HuskieRobotics/HuskieBoardPublic/Eagle CAD/projects/HuskieBoard/PthHeaderAssy.png

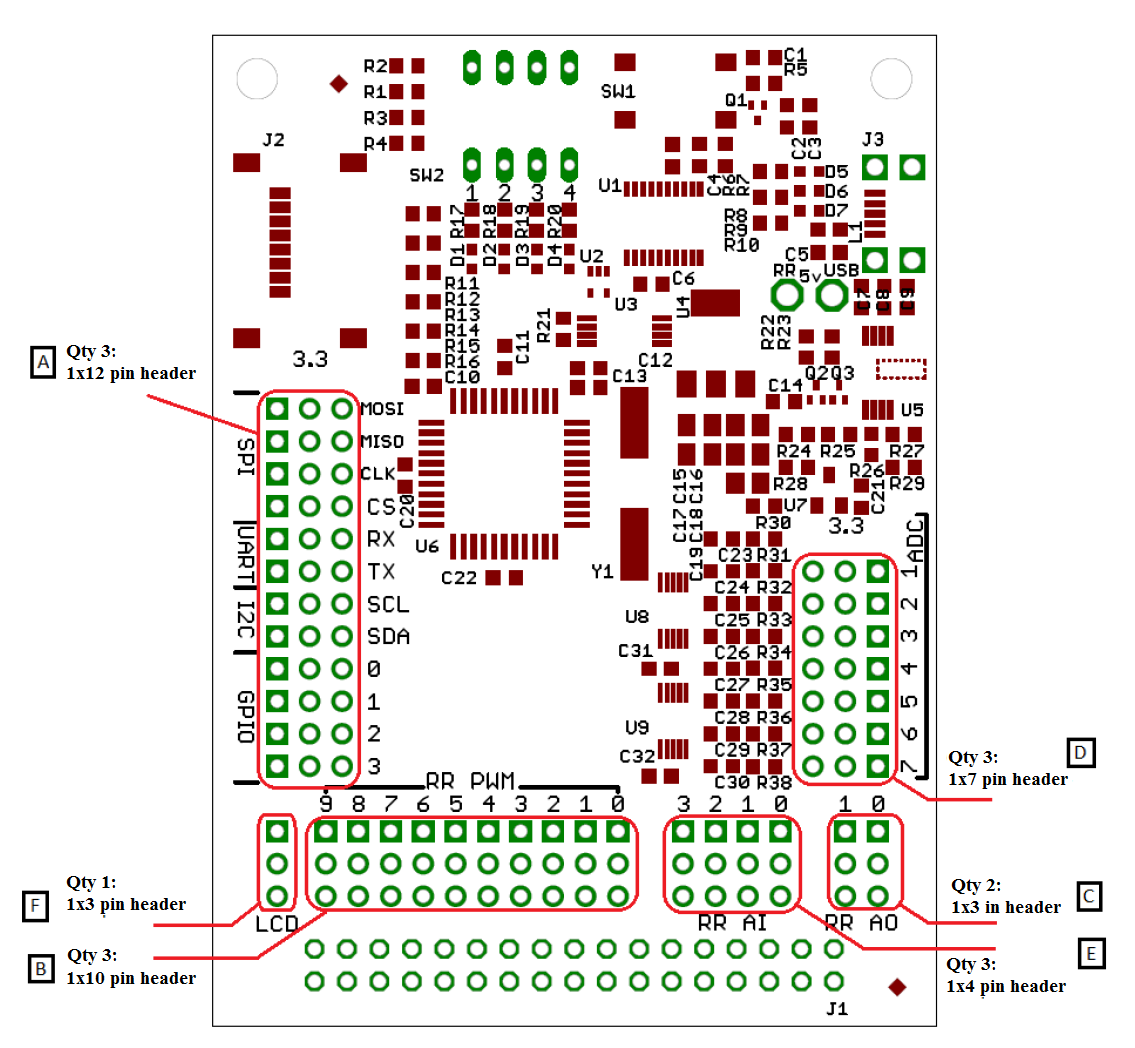
Eagle CAD/projects/HuskieBoard/PthHeaderAssy.png
