HuskieRobotics/HuskieBoardPublic/LabView/LabVIEW API/Examples/LED Example/HB__OpenHuskieBoardp.png

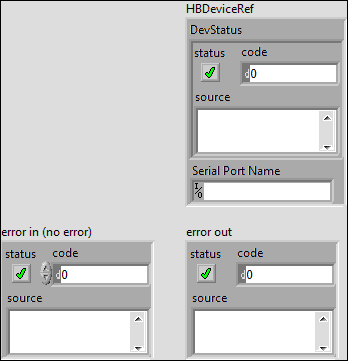
LabView/LabVIEW API/Examples/LED Example/HB__OpenHuskieBoardp.png
