HuskieRobotics/HuskieBoardPublic/LabView/LabVIEW API/Huskie Board/HuskieBoard API Doc/HB_CheckChecksum/HB__CheckChecksumd.png

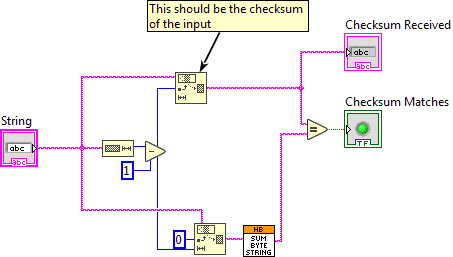
LabView/LabVIEW API/Huskie Board/HuskieBoard API Doc/HB_CheckChecksum/HB__CheckChecksumd.png
