HuskieRobotics/HuskieBoardPublic/LabView/LabVIEW API/Huskie Board/HuskieBoard API Doc/HB_CloseHuskieBoard/HB__CloseHuskieBoardh.png

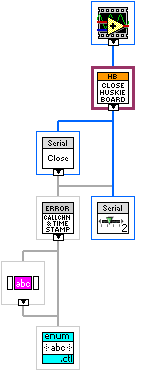
LabView/LabVIEW API/Huskie Board/HuskieBoard API Doc/HB_CloseHuskieBoard/HB__CloseHuskieBoardh.png
