HuskieRobotics/HuskieBoardPublic/LabView/LabVIEW API/Huskie Board/HuskieBoard API Doc/HB_CloseHuskieBoard/HB__CloseHuskieBoardp.png

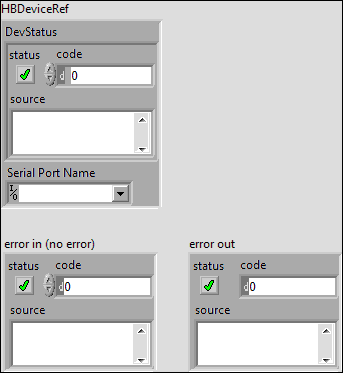
LabView/LabVIEW API/Huskie Board/HuskieBoard API Doc/HB_CloseHuskieBoard/HB__CloseHuskieBoardp.png
