HuskieRobotics/HuskieBoardPublic/LabView/LabVIEW API/Huskie Board/HuskieBoard API Doc/HB_CloseLog/HB__CloseLogd.png

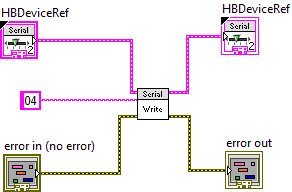
LabView/LabVIEW API/Huskie Board/HuskieBoard API Doc/HB_CloseLog/HB__CloseLogd.png
