HuskieRobotics/HuskieBoardPublic/LabView/LabVIEW API/Huskie Board/HuskieBoard API Doc/HB_CloseLog/HB__CloseLogp.png

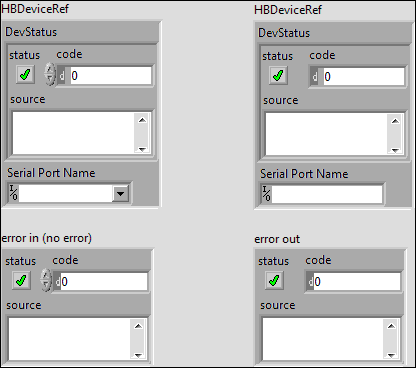
LabView/LabVIEW API/Huskie Board/HuskieBoard API Doc/HB_CloseLog/HB__CloseLogp.png
