HuskieRobotics/HuskieBoardPublic/LabView/LabVIEW API/Huskie Board/HuskieBoard API Doc/HB_ConfigureDIO/HB__ConfigureDIOd2.png

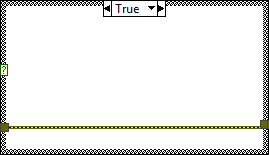
LabView/LabVIEW API/Huskie Board/HuskieBoard API Doc/HB_ConfigureDIO/HB__ConfigureDIOd2.png
