HuskieRobotics/HuskieBoardPublic/LabView/LabVIEW API/Huskie Board/HuskieBoard API Doc/HB_ConfigureDIO/HB__ConfigureDIOd.png

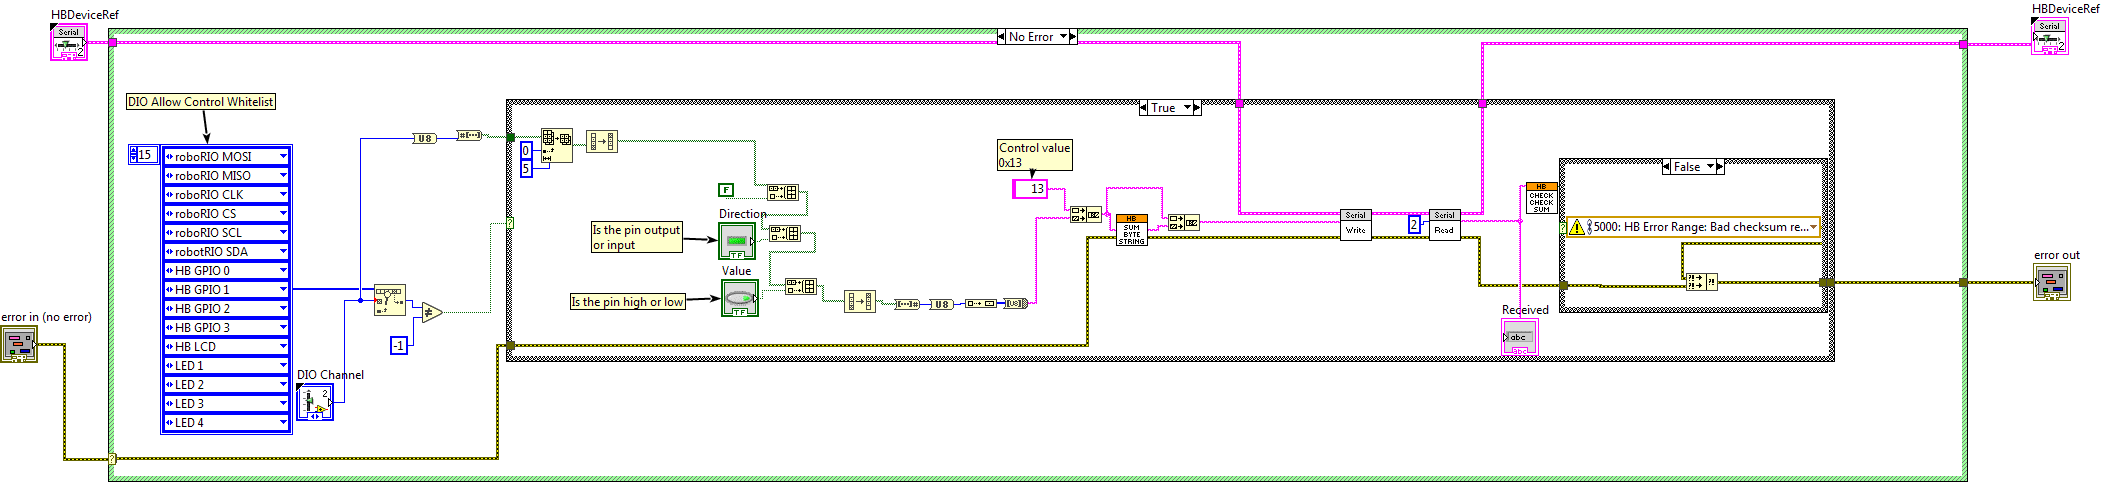
LabView/LabVIEW API/Huskie Board/HuskieBoard API Doc/HB_ConfigureDIO/HB__ConfigureDIOd.png
