HuskieRobotics/HuskieBoardPublic/LabView/LabVIEW API/Huskie Board/HuskieBoard API Doc/HB_ConfigureDIO/HB__ConfigureDIOh.png

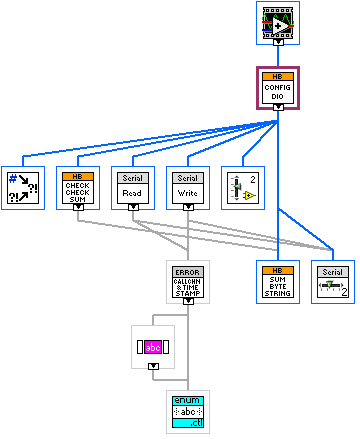
LabView/LabVIEW API/Huskie Board/HuskieBoard API Doc/HB_ConfigureDIO/HB__ConfigureDIOh.png
