HuskieRobotics/HuskieBoardPublic/LabView/LabVIEW API/Huskie Board/HuskieBoard API Doc/HB_ConfigureLED/HB__ConfigureLEDd2.png

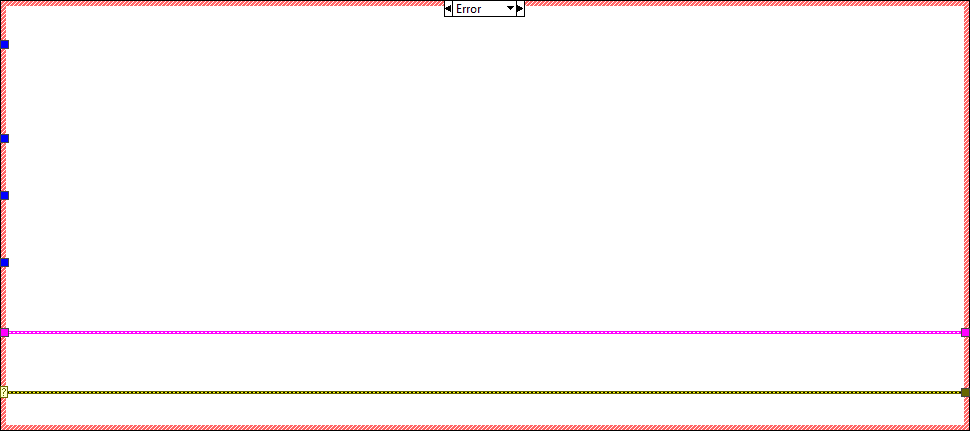
LabView/LabVIEW API/Huskie Board/HuskieBoard API Doc/HB_ConfigureLED/HB__ConfigureLEDd2.png
