HuskieRobotics/HuskieBoardPublic/LabView/LabVIEW API/Huskie Board/HuskieBoard API Doc/HB_ConfigureLED/HB__ConfigureLEDh.png

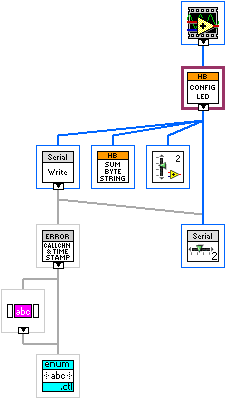
LabView/LabVIEW API/Huskie Board/HuskieBoard API Doc/HB_ConfigureLED/HB__ConfigureLEDh.png
