HuskieRobotics/HuskieBoardPublic/LabView/LabVIEW API/Huskie Board/HuskieBoard API Doc/HB_ConfigureLED/HB__ConfigureLEDp.png

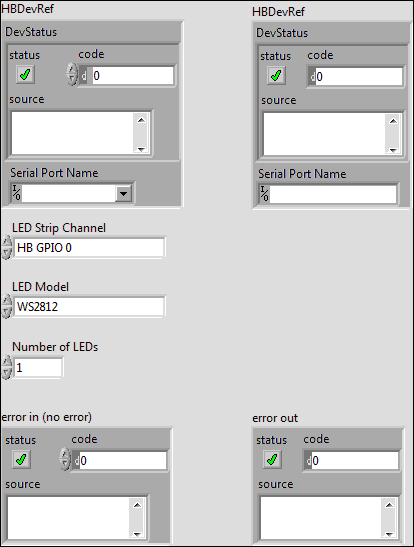
LabView/LabVIEW API/Huskie Board/HuskieBoard API Doc/HB_ConfigureLED/HB__ConfigureLEDp.png
