HuskieRobotics/HuskieBoardPublic/LabView/LabVIEW API/Huskie Board/HuskieBoard API Doc/HB_DisplayLCD/HB__DisplayLCDd4.png

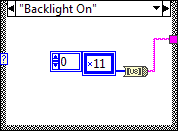
LabView/LabVIEW API/Huskie Board/HuskieBoard API Doc/HB_DisplayLCD/HB__DisplayLCDd4.png
