HuskieRobotics/HuskieBoardPublic/LabView/LabVIEW API/Huskie Board/HuskieBoard API Doc/HB_DisplayLCD/HB__DisplayLCDd.png

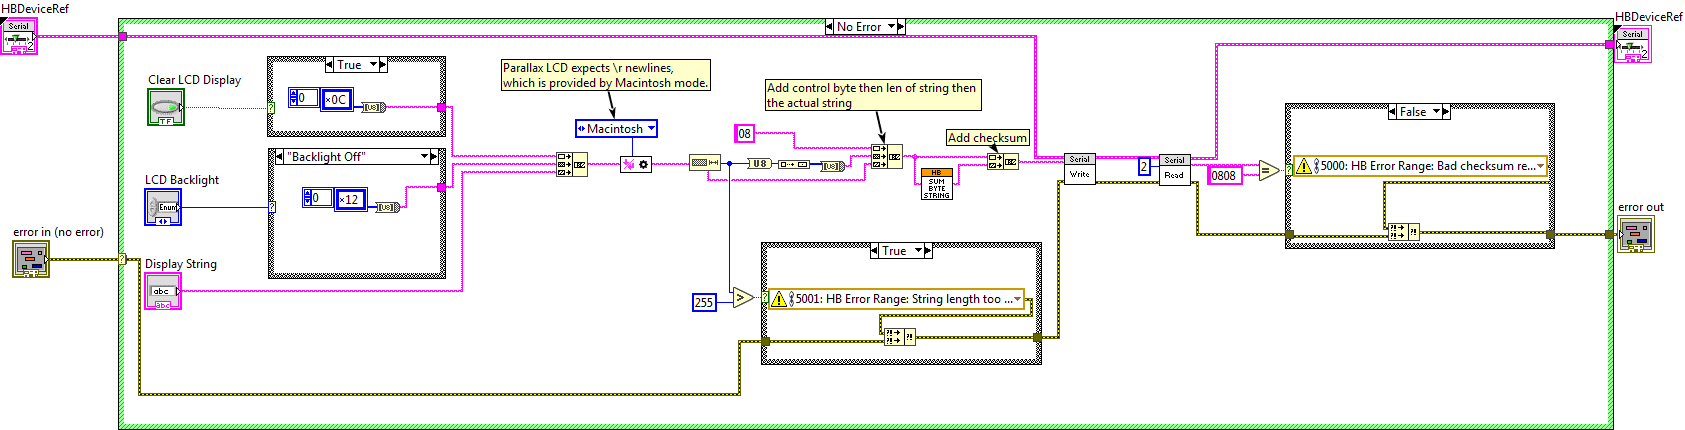
LabView/LabVIEW API/Huskie Board/HuskieBoard API Doc/HB_DisplayLCD/HB__DisplayLCDd.png
