HuskieRobotics/HuskieBoardPublic/LabView/LabVIEW API/Huskie Board/HuskieBoard API Doc/HB_DisplayLCD/HB__DisplayLCDh.png

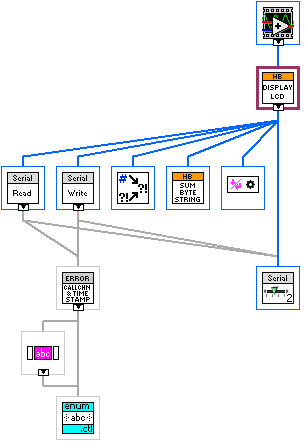
LabView/LabVIEW API/Huskie Board/HuskieBoard API Doc/HB_DisplayLCD/HB__DisplayLCDh.png
