HuskieRobotics/HuskieBoardPublic/LabView/LabVIEW API/Huskie Board/HuskieBoard API Doc/HB_GetFirmwareVersion/HB__GetFirmwareVersiond1.png

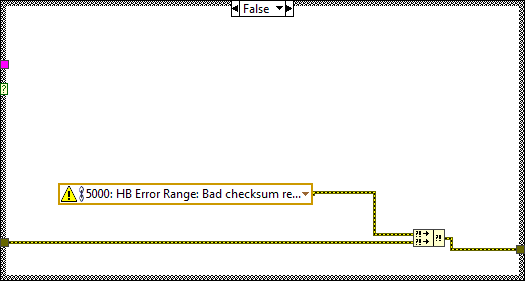
LabView/LabVIEW API/Huskie Board/HuskieBoard API Doc/HB_GetFirmwareVersion/HB__GetFirmwareVersiond1.png
