HuskieRobotics/HuskieBoardPublic/LabView/LabVIEW API/Huskie Board/HuskieBoard API Doc/HB_GetFirmwareVersion/HB__GetFirmwareVersionp.png

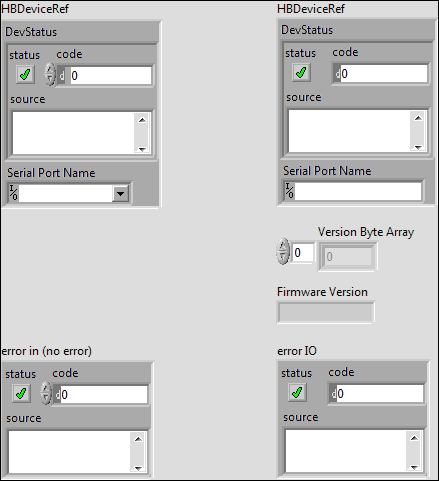
LabView/LabVIEW API/Huskie Board/HuskieBoard API Doc/HB_GetFirmwareVersion/HB__GetFirmwareVersionp.png
