HuskieRobotics/HuskieBoardPublic/LabView/LabVIEW API/Huskie Board/HuskieBoard API Doc/HB_OpenHuskieBoard/HB__OpenHuskieBoardh.png

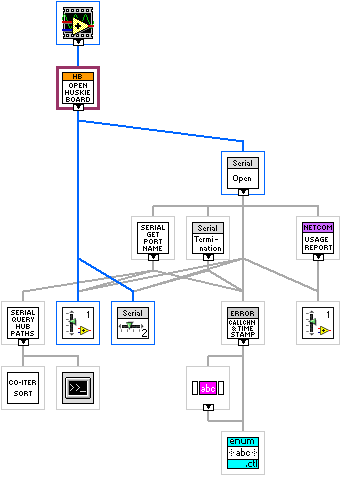
LabView/LabVIEW API/Huskie Board/HuskieBoard API Doc/HB_OpenHuskieBoard/HB__OpenHuskieBoardh.png
