HuskieRobotics/HuskieBoardPublic/LabView/LabVIEW API/Huskie Board/HuskieBoard API Doc/HB_OpenLog/HB__OpenLogd2.png

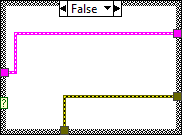
LabView/LabVIEW API/Huskie Board/HuskieBoard API Doc/HB_OpenLog/HB__OpenLogd2.png
