HuskieRobotics/HuskieBoardPublic/LabView/LabVIEW API/Huskie Board/HuskieBoard API Doc/HB_OpenLog/HB__OpenLogd.png

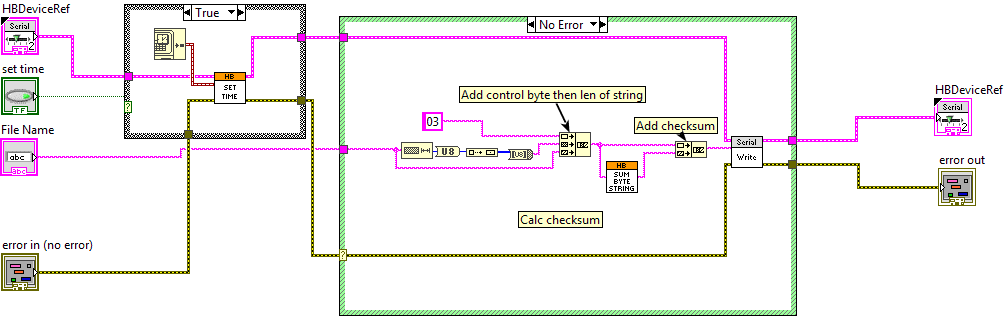
LabView/LabVIEW API/Huskie Board/HuskieBoard API Doc/HB_OpenLog/HB__OpenLogd.png
