HuskieRobotics/HuskieBoardPublic/LabView/LabVIEW API/Huskie Board/HuskieBoard API Doc/HB_ReadAIAllChannels/HB__ReadAIAllChannelsd1.png

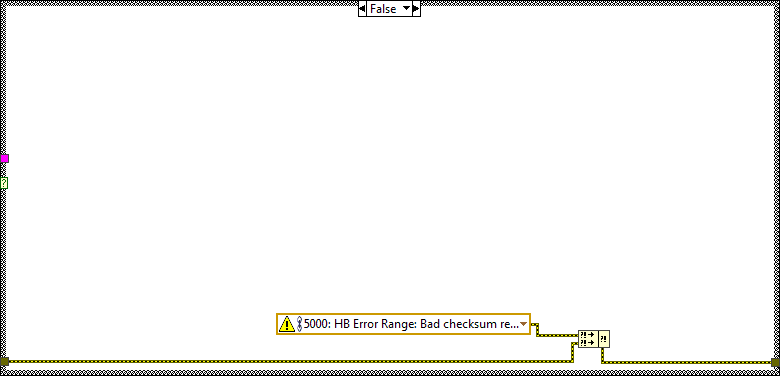
LabView/LabVIEW API/Huskie Board/HuskieBoard API Doc/HB_ReadAIAllChannels/HB__ReadAIAllChannelsd1.png
