HuskieRobotics/HuskieBoardPublic/LabView/LabVIEW API/Huskie Board/HuskieBoard API Doc/HB_ReadAIAllChannels/HB__ReadAIAllChannelsh.png

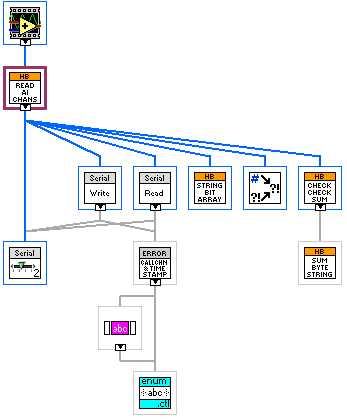
LabView/LabVIEW API/Huskie Board/HuskieBoard API Doc/HB_ReadAIAllChannels/HB__ReadAIAllChannelsh.png
