HuskieRobotics/HuskieBoardPublic/LabView/LabVIEW API/Huskie Board/HuskieBoard API Doc/HB_ReadAIAllChannels/HB__ReadAIAllChannelsp.png

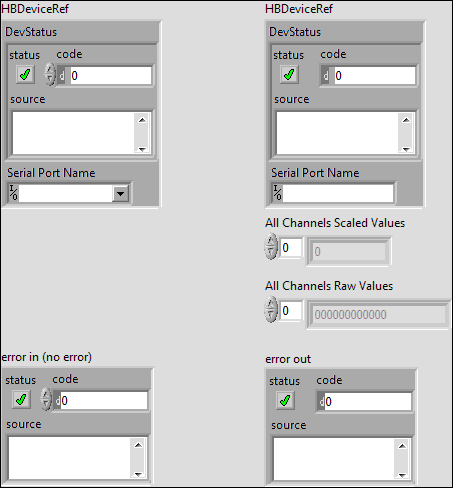
LabView/LabVIEW API/Huskie Board/HuskieBoard API Doc/HB_ReadAIAllChannels/HB__ReadAIAllChannelsp.png
