HuskieRobotics/HuskieBoardPublic/LabView/LabVIEW API/Huskie Board/HuskieBoard API Doc/HB_ReadAISingleChannel/HB__ReadAISingleChanneld1.png

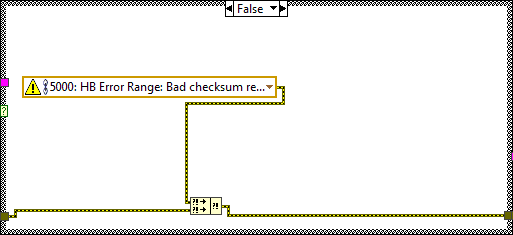
LabView/LabVIEW API/Huskie Board/HuskieBoard API Doc/HB_ReadAISingleChannel/HB__ReadAISingleChanneld1.png
