HuskieRobotics/HuskieBoardPublic/LabView/LabVIEW API/Huskie Board/HuskieBoard API Doc/HB_ReadAISingleChannel/HB__ReadAISingleChannelp.png

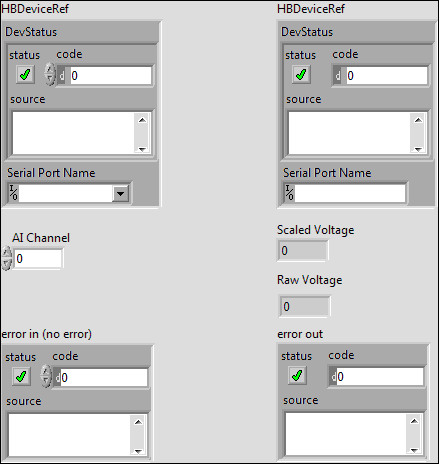
LabView/LabVIEW API/Huskie Board/HuskieBoard API Doc/HB_ReadAISingleChannel/HB__ReadAISingleChannelp.png
