HuskieRobotics/HuskieBoardPublic/LabView/LabVIEW API/Huskie Board/HuskieBoard API Doc/HB_ReadDIOAllChannels/HB__ReadDIOAllChannelsh.png

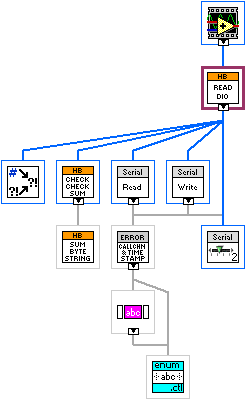
LabView/LabVIEW API/Huskie Board/HuskieBoard API Doc/HB_ReadDIOAllChannels/HB__ReadDIOAllChannelsh.png
