HuskieRobotics/HuskieBoardPublic/LabView/LabVIEW API/Huskie Board/HuskieBoard API Doc/HB_ReadDIOAllChannels/HB__ReadDIOAllChannelsp.png

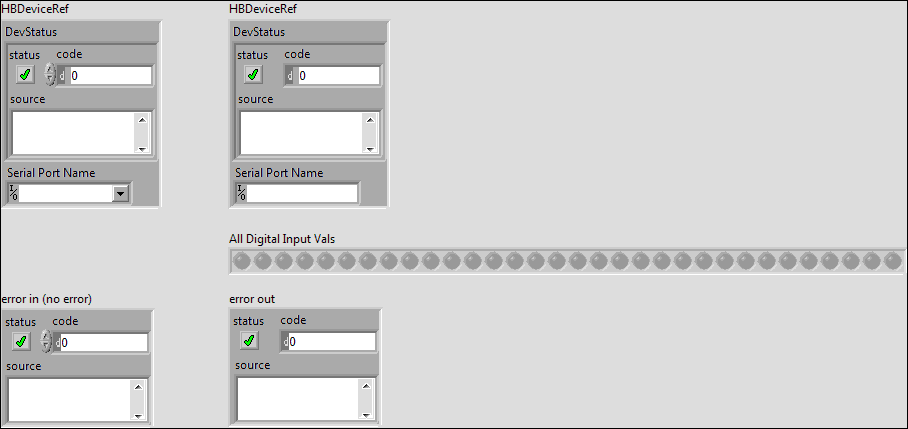
LabView/LabVIEW API/Huskie Board/HuskieBoard API Doc/HB_ReadDIOAllChannels/HB__ReadDIOAllChannelsp.png
