HuskieRobotics/HuskieBoardPublic/LabView/LabVIEW API/Huskie Board/HuskieBoard API Doc/HB_RefNumRegistryGet/HB__RefNumRegistryGetd.png

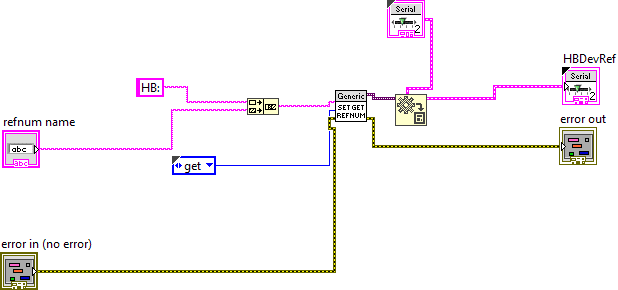
LabView/LabVIEW API/Huskie Board/HuskieBoard API Doc/HB_RefNumRegistryGet/HB__RefNumRegistryGetd.png
