HuskieRobotics/HuskieBoardPublic/LabView/LabVIEW API/Huskie Board/HuskieBoard API Doc/HB_RefNumRegistryGet/HB__RefNumRegistryGetp.png

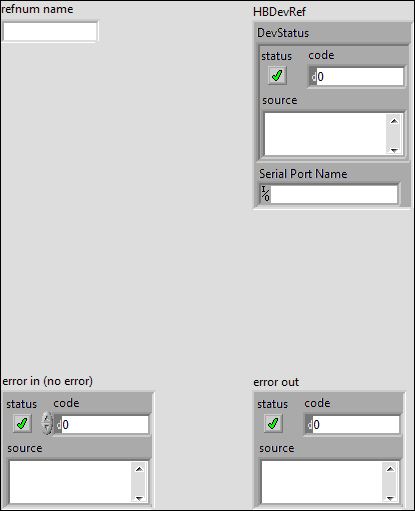
LabView/LabVIEW API/Huskie Board/HuskieBoard API Doc/HB_RefNumRegistryGet/HB__RefNumRegistryGetp.png
