HuskieRobotics/HuskieBoardPublic/LabView/LabVIEW API/Huskie Board/HuskieBoard API Doc/HB_RefNumRegistrySet/HB__RefNumRegistrySetd.png

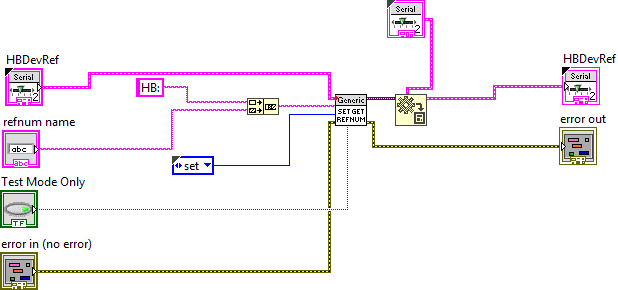
LabView/LabVIEW API/Huskie Board/HuskieBoard API Doc/HB_RefNumRegistrySet/HB__RefNumRegistrySetd.png
