HuskieRobotics/HuskieBoardPublic/LabView/LabVIEW API/Huskie Board/HuskieBoard API Doc/HB_RefNumRegistrySet/HB__RefNumRegistrySetp.png

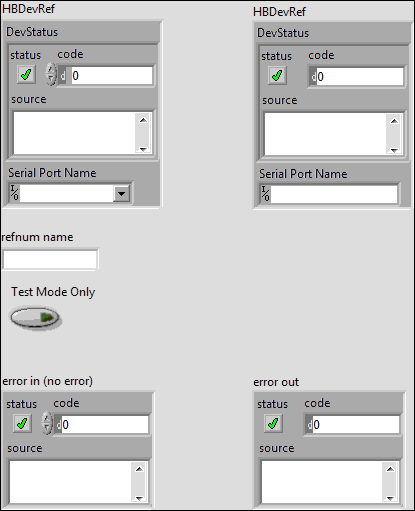
LabView/LabVIEW API/Huskie Board/HuskieBoard API Doc/HB_RefNumRegistrySet/HB__RefNumRegistrySetp.png
