HuskieRobotics/HuskieBoardPublic/LabView/LabVIEW API/Huskie Board/HuskieBoard API Doc/HB_SetLEDIntensity/HB__SetLEDIntensityd1.png

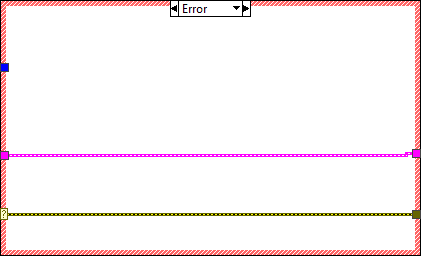
LabView/LabVIEW API/Huskie Board/HuskieBoard API Doc/HB_SetLEDIntensity/HB__SetLEDIntensityd1.png
