HuskieRobotics/HuskieBoardPublic/LabView/LabVIEW API/Huskie Board/HuskieBoard API Doc/HB_SetLEDIntensity/HB__SetLEDIntensityd.png

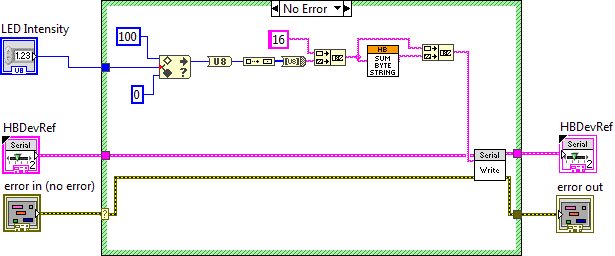
LabView/LabVIEW API/Huskie Board/HuskieBoard API Doc/HB_SetLEDIntensity/HB__SetLEDIntensityd.png
