HuskieRobotics/HuskieBoardPublic/LabView/LabVIEW API/Huskie Board/HuskieBoard API Doc/HB_SetLEDIntensity/HB__SetLEDIntensityh.png

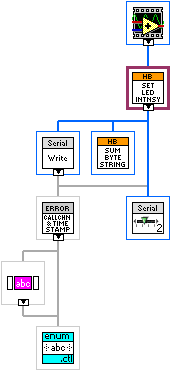
LabView/LabVIEW API/Huskie Board/HuskieBoard API Doc/HB_SetLEDIntensity/HB__SetLEDIntensityh.png
