HuskieRobotics/HuskieBoardPublic/LabView/LabVIEW API/Huskie Board/HuskieBoard API Doc/HB_SetLEDIntensity/HB__SetLEDIntensityp.png

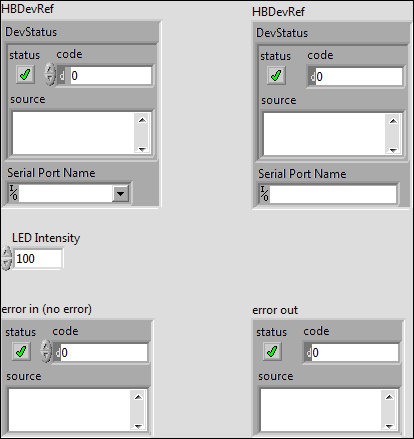
LabView/LabVIEW API/Huskie Board/HuskieBoard API Doc/HB_SetLEDIntensity/HB__SetLEDIntensityp.png
