HuskieRobotics/HuskieBoardPublic/LabView/LabVIEW API/Huskie Board/HuskieBoard API Doc/HB_SetLEDRGBValue/HB__SetLEDRGBValued.png

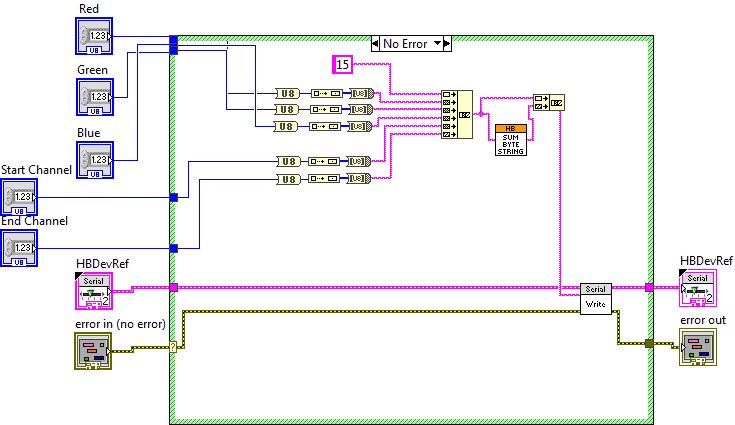
LabView/LabVIEW API/Huskie Board/HuskieBoard API Doc/HB_SetLEDRGBValue/HB__SetLEDRGBValued.png
