HuskieRobotics/HuskieBoardPublic/LabView/LabVIEW API/Huskie Board/HuskieBoard API Doc/HB_SetTime/HB__SetTimep.png

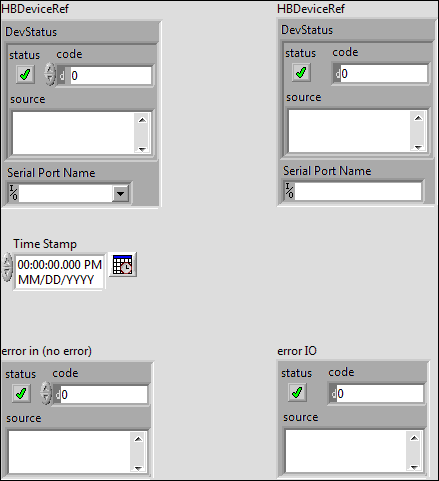
LabView/LabVIEW API/Huskie Board/HuskieBoard API Doc/HB_SetTime/HB__SetTimep.png
