HuskieRobotics/HuskieBoardPublic/LabView/LabVIEW API/Huskie Board/HuskieBoard API Doc/HB_StringToBitArray/HB__StringToBitArrayd.png

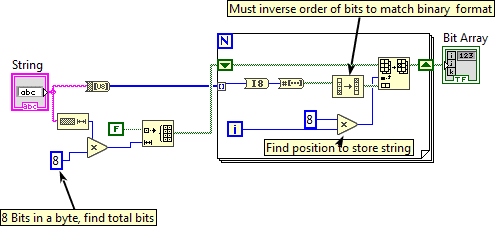
LabView/LabVIEW API/Huskie Board/HuskieBoard API Doc/HB_StringToBitArray/HB__StringToBitArrayd.png
