HuskieRobotics/HuskieBoardPublic/LabView/LabVIEW API/Huskie Board/HuskieBoard API Doc/HB_SumStringOfBytes/HB__SumStringOfBytesd.png

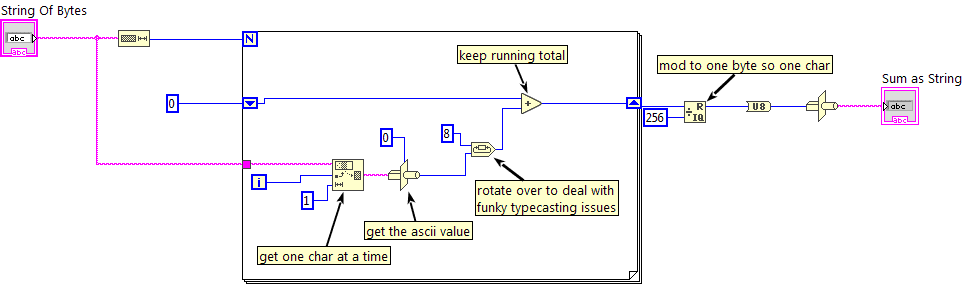
LabView/LabVIEW API/Huskie Board/HuskieBoard API Doc/HB_SumStringOfBytes/HB__SumStringOfBytesd.png
