HuskieRobotics/HuskieBoardPublic/LabView/LabVIEW API/Huskie Board/HuskieBoard API Doc/HB_WriteToLog/HB__WriteToLogd.png

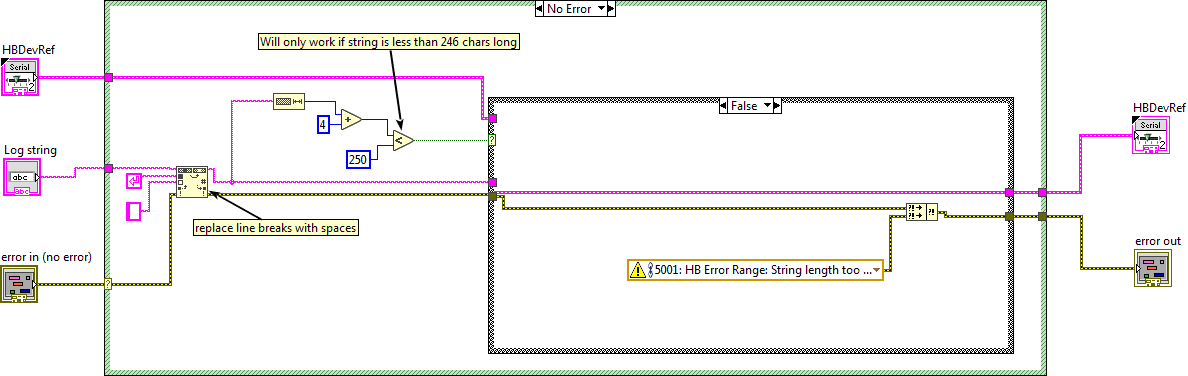
LabView/LabVIEW API/Huskie Board/HuskieBoard API Doc/HB_WriteToLog/HB__WriteToLogd.png
