HuskieRobotics/HuskieBoardPublic/Eagle CAD/projects/HuskieBoard/RoboRio Expansion Board V2 11-26-2015.pdf

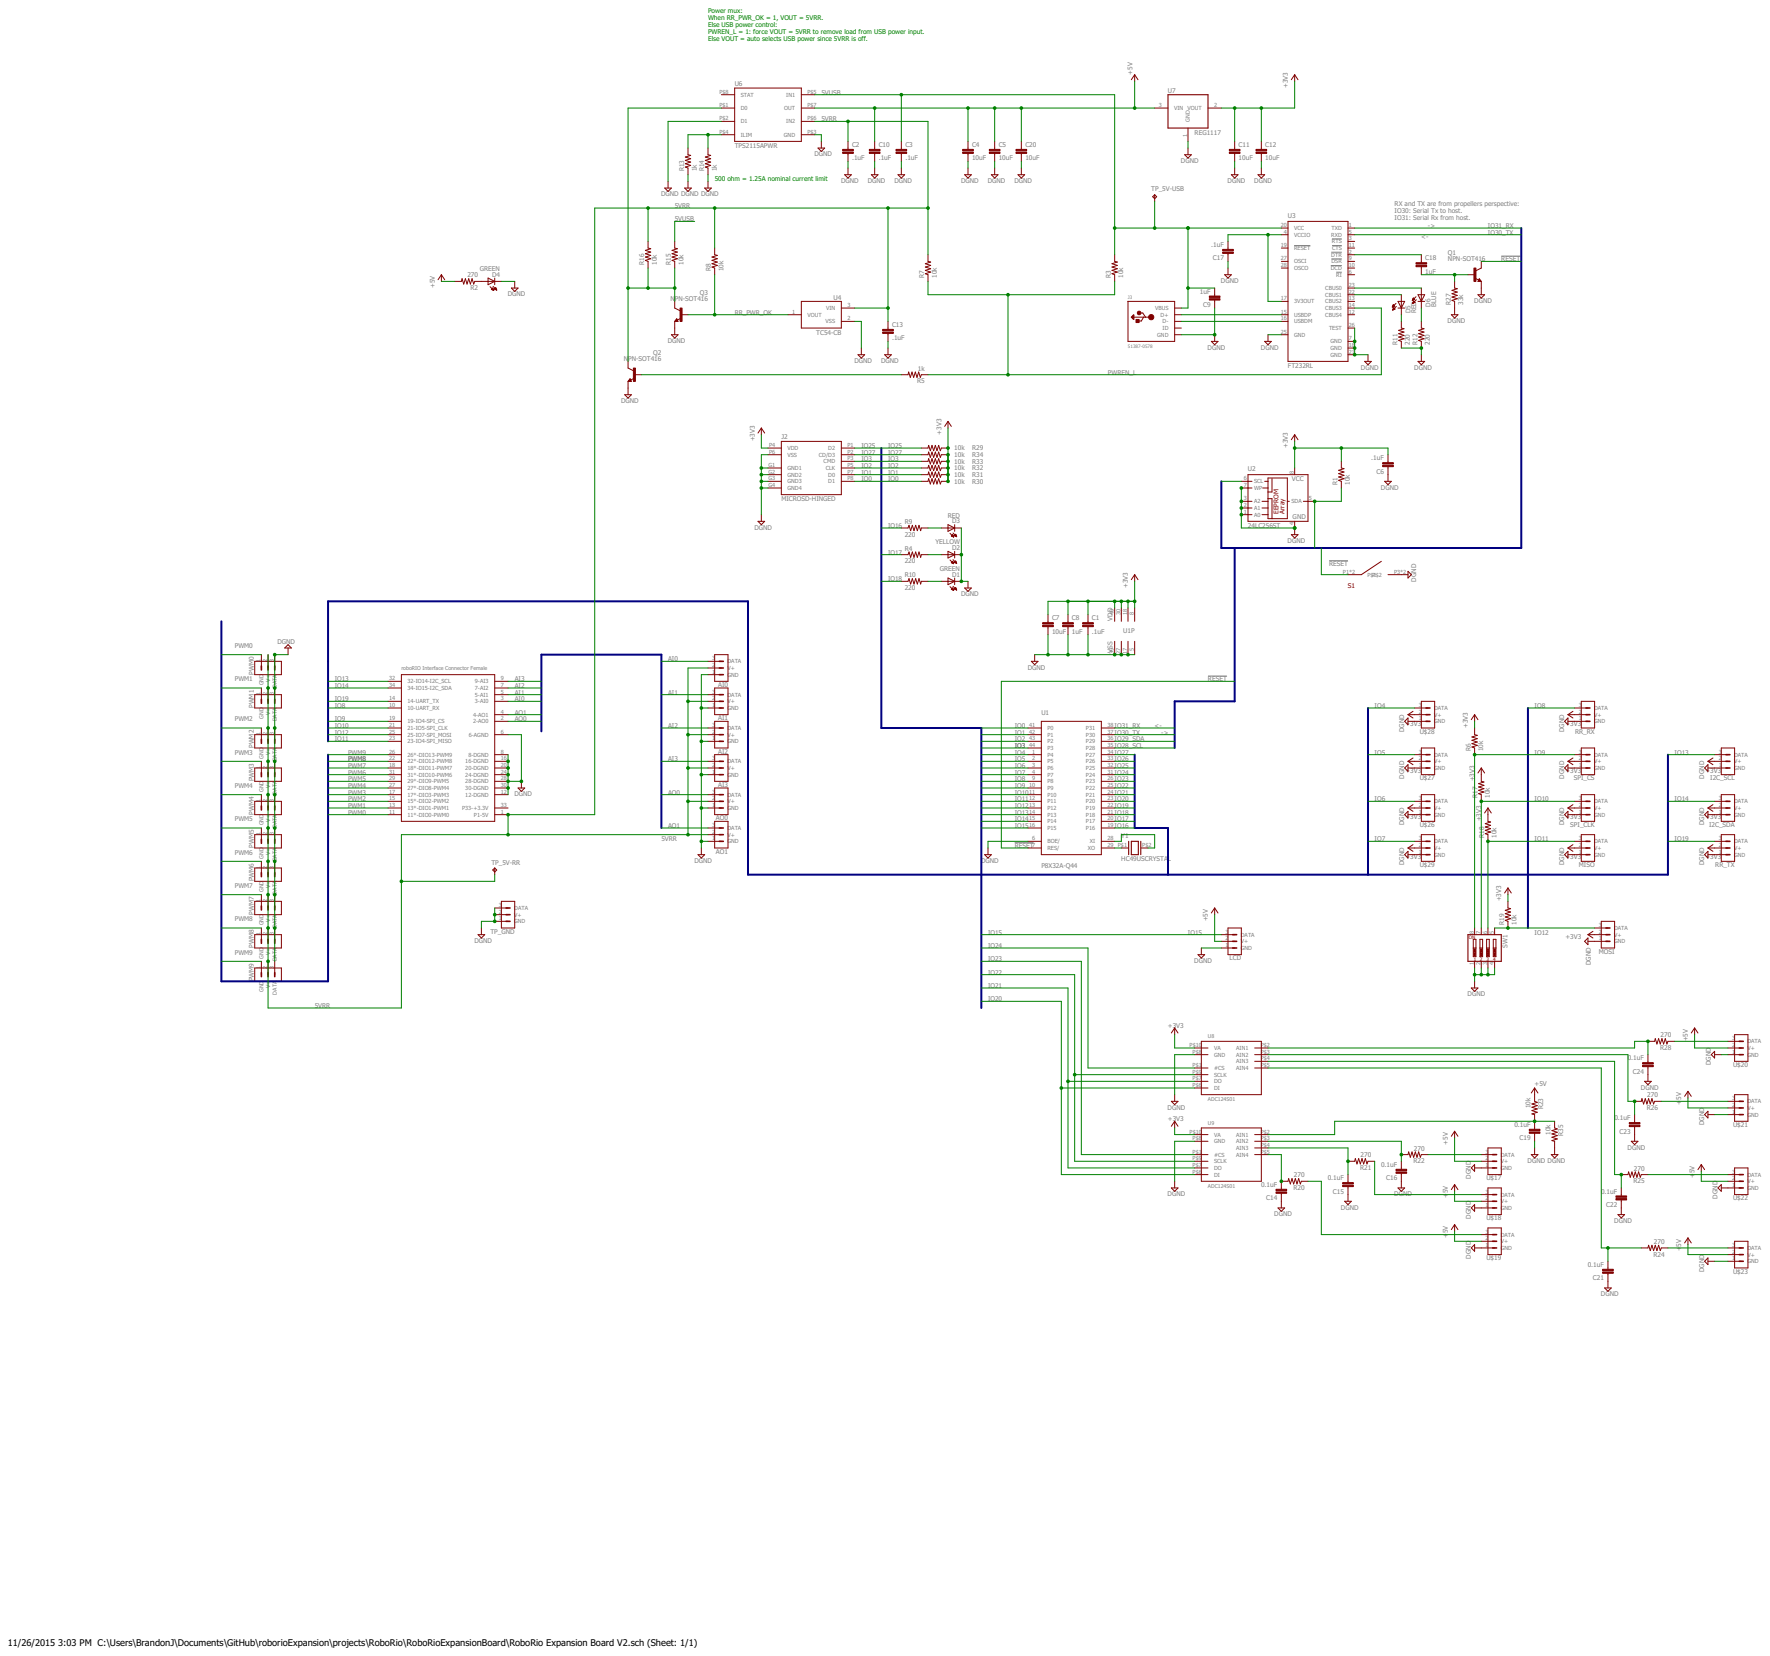
[picture p71: page 1]
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

500 ohm = 1.25A nominal current limit

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

roboRIO Interface Connector Female

+3V3 DGND +3V3 DGND +3V3 DGND +3V3 DGND +3V3 DGND

DGND

11/26/2015 3:03 PM C:\Users\BrandonJ\Documents\GitHub\roborioExpansion\projects\RoboRio\RoboRioExpansionBoard\RoboRio Expansion Board V2.sch (Sheet: 1/1)
