HuskieRobotics/HuskieBoardPublic/Eagle CAD/projects/HuskieBoard/RoboRio Expansion Board V2 bottom.pdf

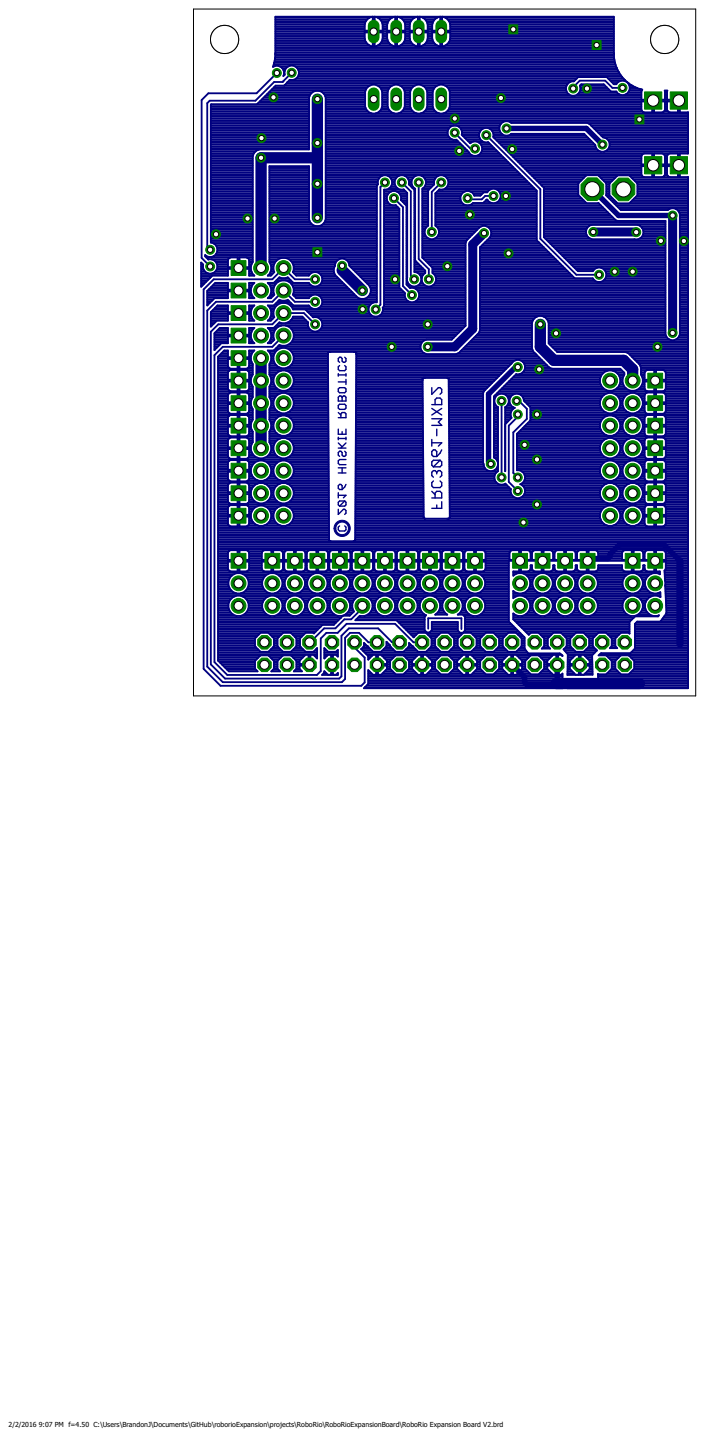
[picture p72: page 1]

2/2/2016 9:07 PM f=4.50 C:\Users\BrandonJ\Documents\GitHub\roborioExpansion\projects\RoboRio\RoboRioExpansionBoard\RoboRio Expansion Board V2.brd
