HuskieRobotics/HuskieBoardPublic/Eagle CAD/projects/HuskieBoard/RoboRio Expansion Board V2 brd 1-5-2016.pdf

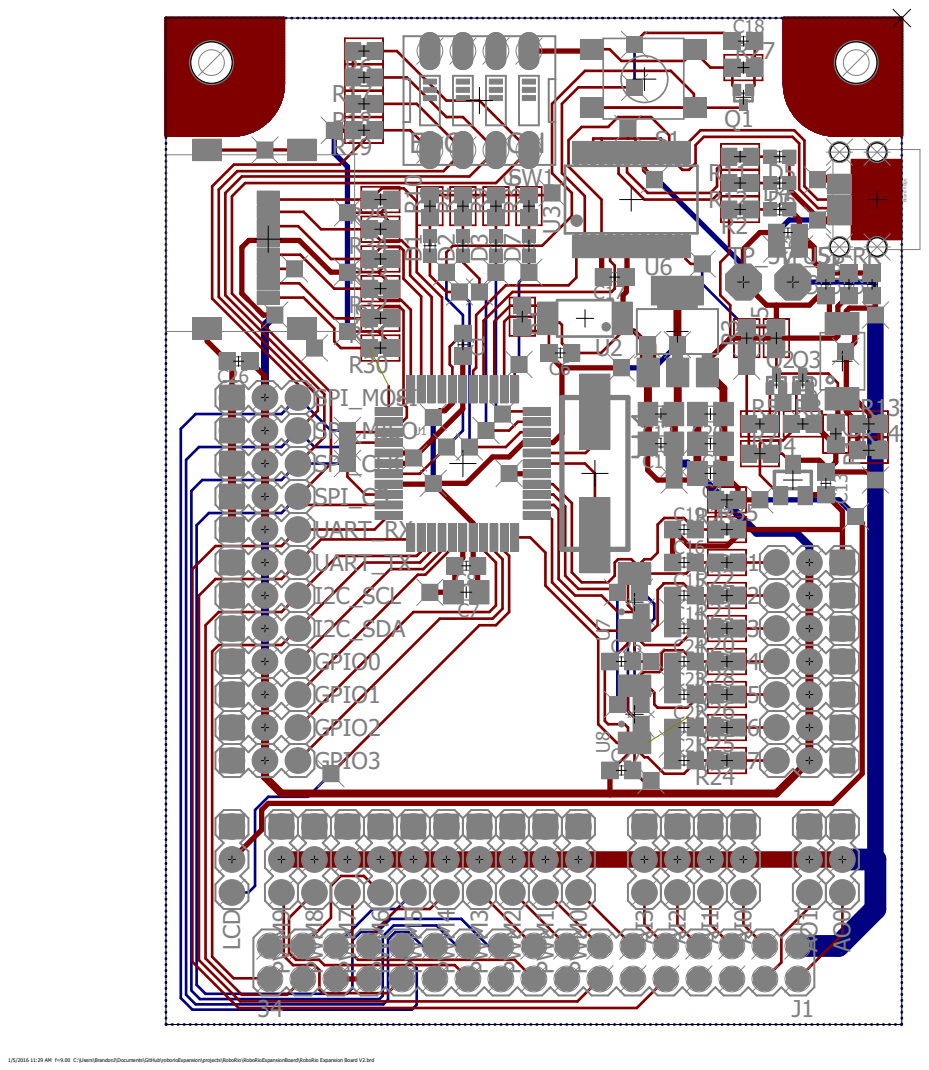
[picture p73: page 1]

1/5/2016 11:29 AM f=9.00 C:\Users\BrandonJ\Documents\GitHub\roborioExpansion\projects\RoboRio\RoboRioExpansionBoard\RoboRio Expansion Board V2.brd
