HuskieRobotics/HuskieBoardPublic/Eagle CAD/projects/HuskieBoard/topfinal.pdf

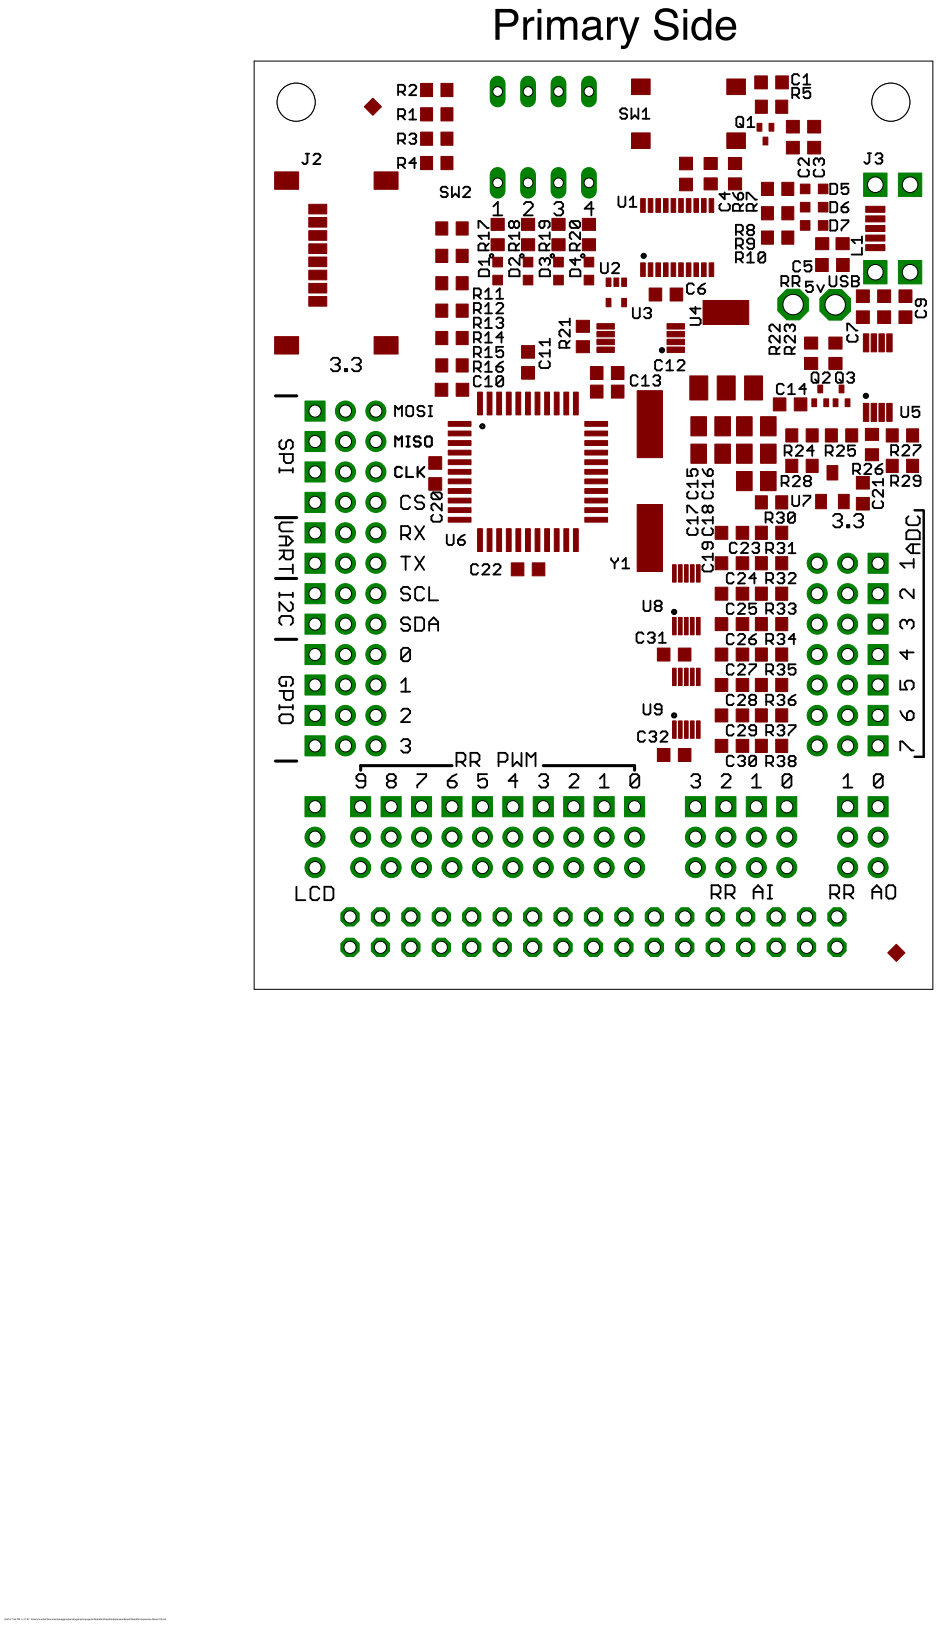
[picture p78: page 1]
