HuskieRobotics/HuskieBoardPublic/Eagle CAD/projects/HuskieBoard/hole chart.pdf

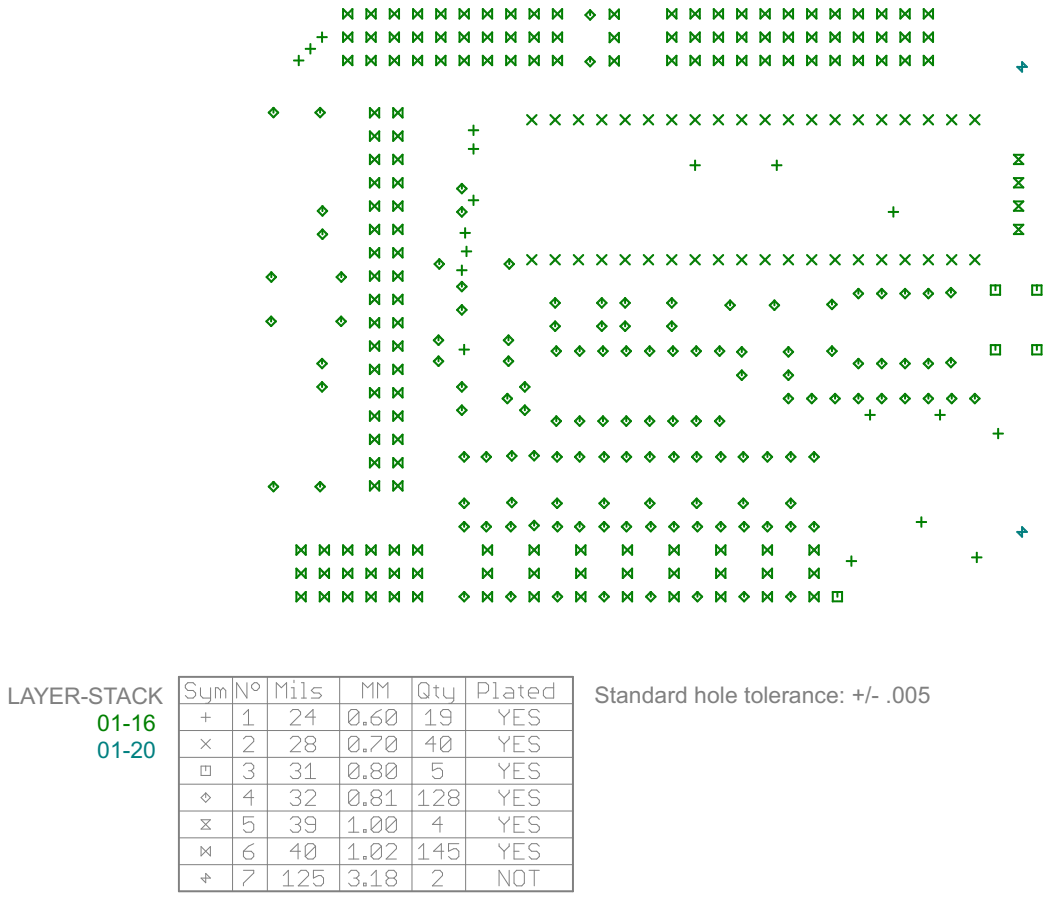
[picture p79: page 1]
